Trikkitt/ArmageddonLightshow/Electronics/PXL_20241116_201726704.jpg

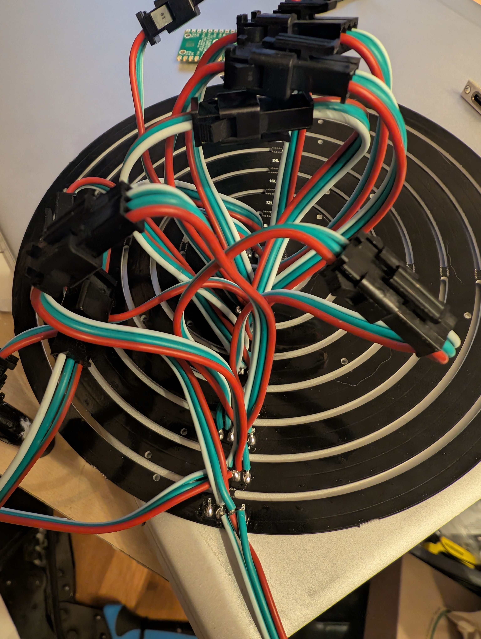
Electronics/PXL_20241116_201726704.jpg
