Trikkitt/ArmageddonLightshow/Electronics/PXL_20241116_205720398.jpg

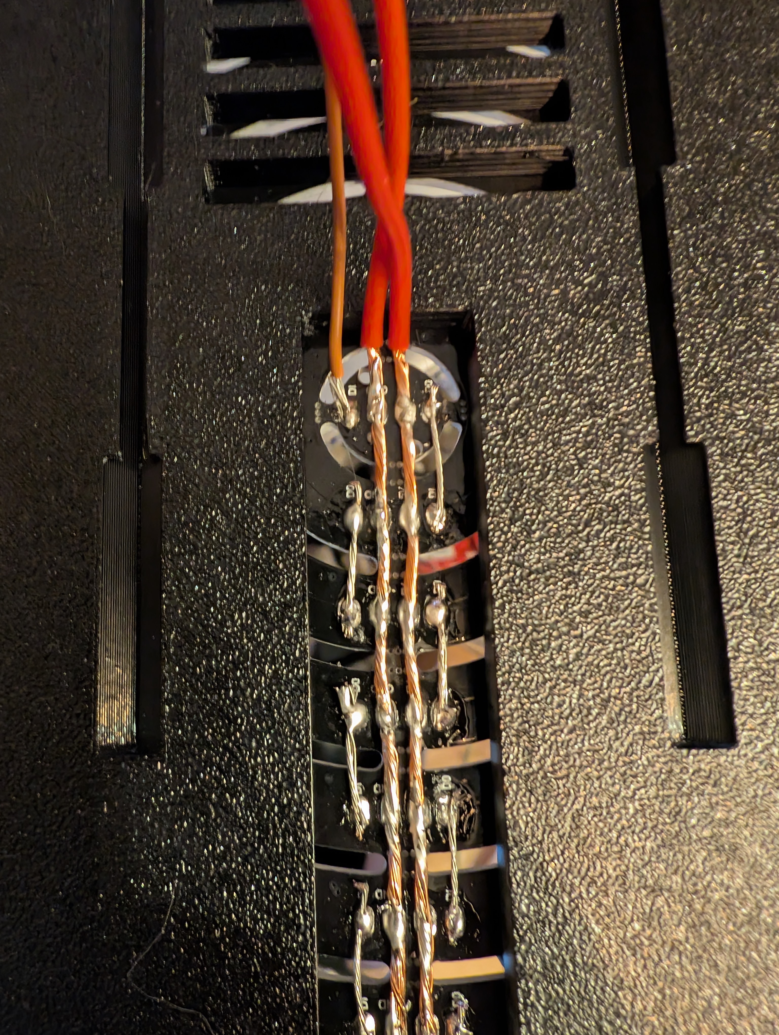
Electronics/PXL_20241116_205720398.jpg
