Trikkitt/ArmageddonLightshow/PXL_20241114_235158370.jpg

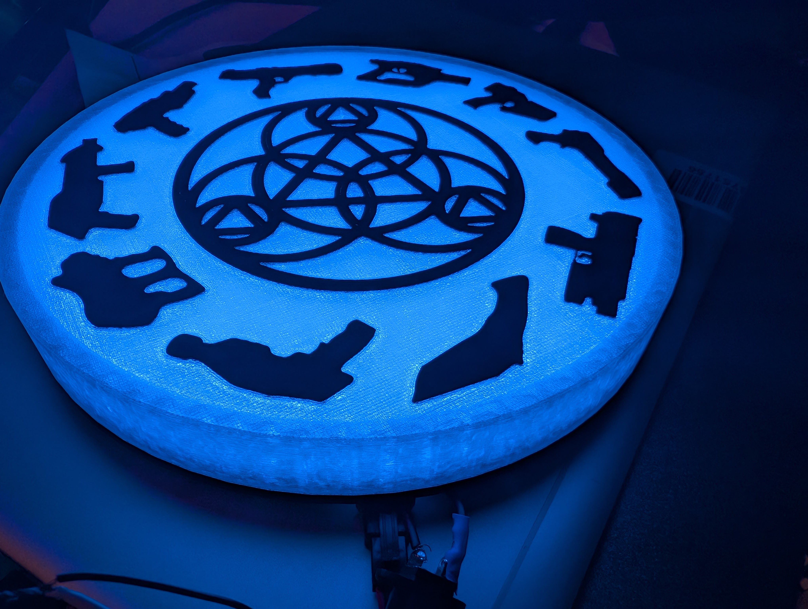
PXL_20241114_235158370.jpg
