Trikkitt/ArmageddonLightshow/SourceMedia/ActualReality Phaser - Mono.bmp

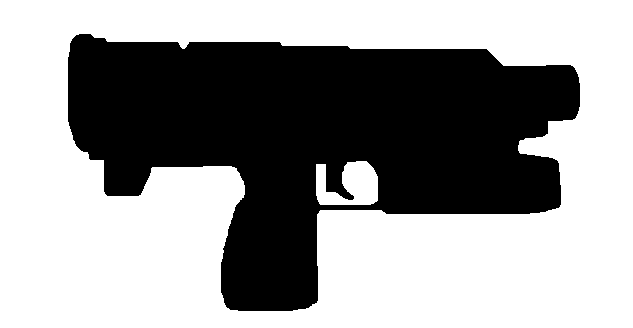
SourceMedia/ActualReality Phaser - Mono.bmp
