Trikkitt/ArmageddonLightshow/SourceMedia/Darklight Phaser1.bmp

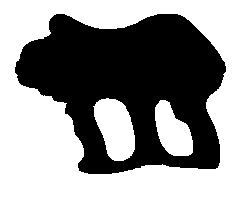
SourceMedia/Darklight Phaser1.bmp
