Trikkitt/ArmageddonLightshow/SourceMedia/Darklight Phaser1.jpg

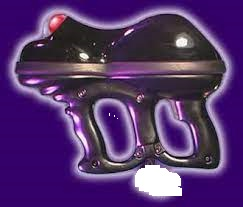
SourceMedia/Darklight Phaser1.jpg
