Trikkitt/ArmageddonLightshow/SourceMedia/Gen7 Phaser.bmp

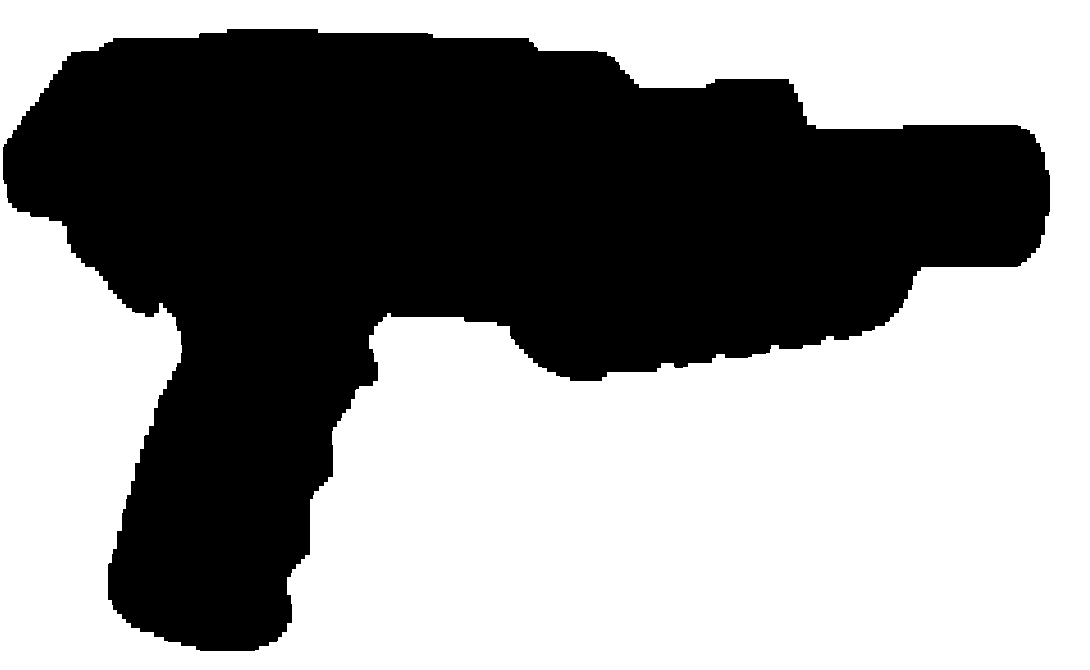
SourceMedia/Gen7 Phaser.bmp
