Trikkitt/ArmageddonLightshow/SourceMedia/Gen7 Phaser.png

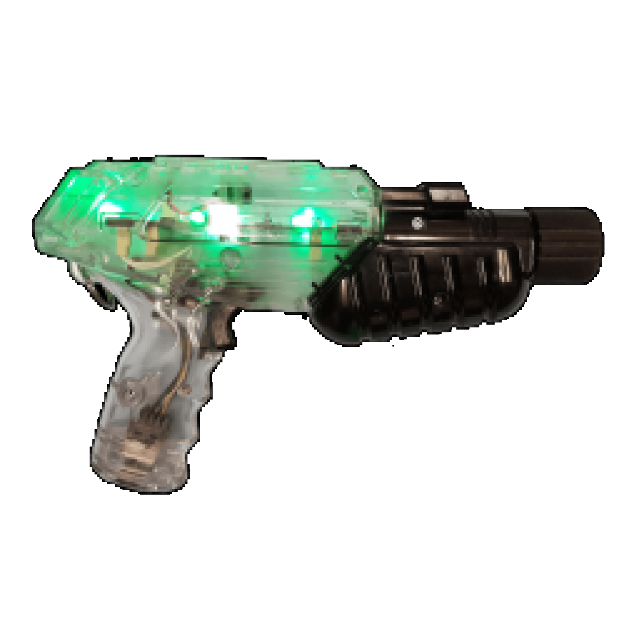
SourceMedia/Gen7 Phaser.png
