Trikkitt/ArmageddonLightshow/SourceMedia/HeliosPhaser.bmp

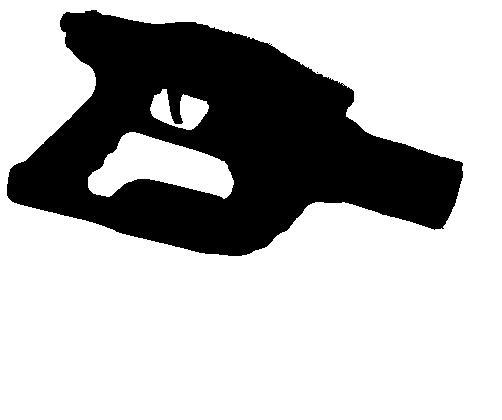
SourceMedia/HeliosPhaser.bmp
