Trikkitt/ArmageddonLightshow/SourceMedia/HeliosPhaser.png

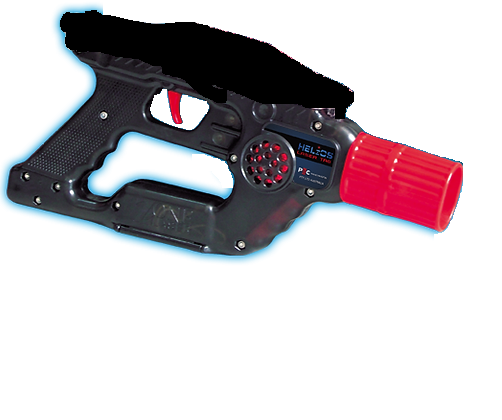
SourceMedia/HeliosPhaser.png
