Trikkitt/ArmageddonLightshow/SourceMedia/LaserBlast Phaser.bmp

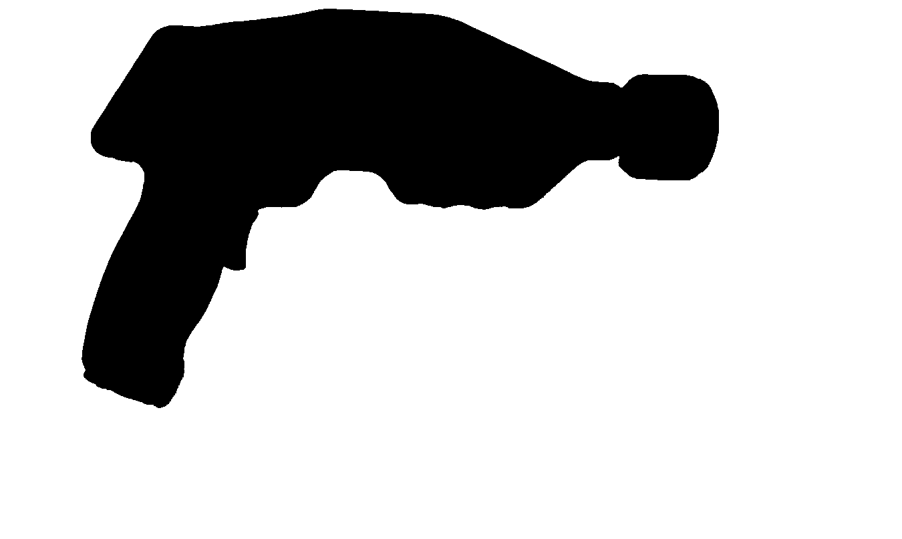
SourceMedia/LaserBlast Phaser.bmp
