Trikkitt/ArmageddonLightshow/SourceMedia/LaserQuestPhaser.bmp

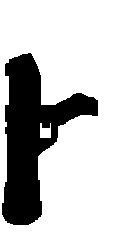
SourceMedia/LaserQuestPhaser.bmp
