Trikkitt/ArmageddonLightshow/SourceMedia/QuasarPhaserOutline.bmp

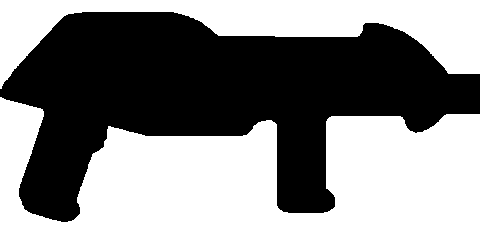
SourceMedia/QuasarPhaserOutline.bmp
