Trikkitt/ArmageddonLightshow/SourceMedia/TronPhaser1.bmp

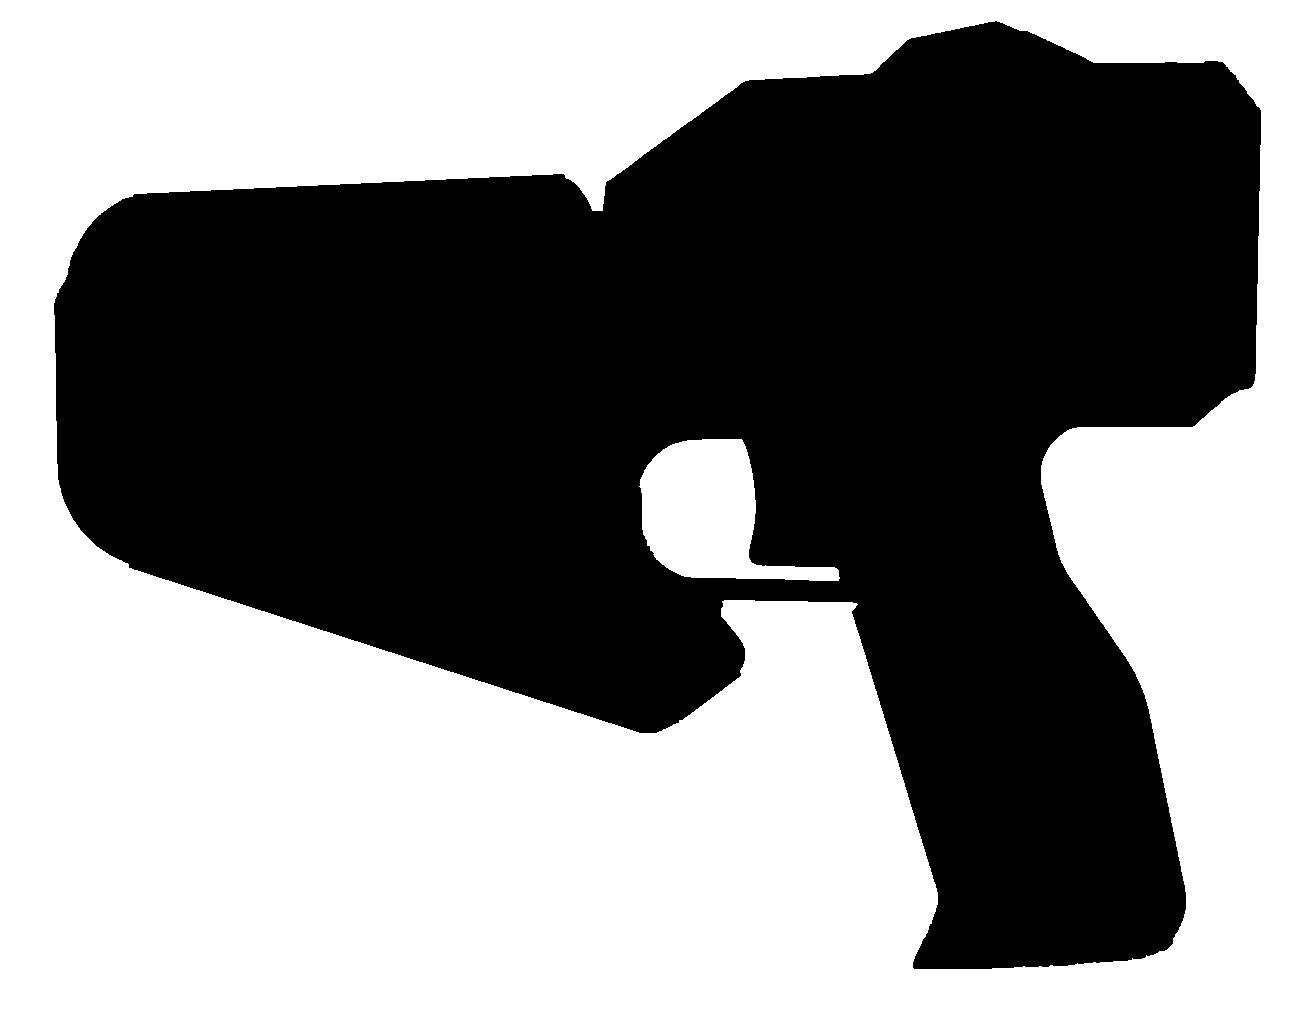
SourceMedia/TronPhaser1.bmp
